BuzzerBox/BuzzController/code/src/rpi_communication.hpp

#ifndef rpi_comm_h
#define rpi_comm_h

#include <Arduino.h>

typedef enum {   
  NO_CONNECTION = 0,
  JUST_CONNECTED = 1,
  CONNECTED = 2,
  JUST_TIMED_OUT = 3,
} Pi_connection_state_t;

typedef struct cmd {
  byte command;
  byte data;
}PiCmd;

class RpiComm {
 public:
  RpiComm(int heartbeatTimeout = 6000);
  boolean checkData();
  void sendUnlock();
  void sendButtonSelected(uint8_t buttonID);
  void sendRawData(byte data);
  Pi_connection_state_t getConnectionState();
  Pi_connection_state_t advanceConnectionState();
  void setConnectionState(Pi_connection_state_t state);
  void heartbeatDetected();
  bool isTimedOut();
  PiCmd getLastCmd();

 private:
  Pi_connection_state_t connection_state;
  unsigned long lastConnection;
  int heartbeatTimeout;
  PiCmd current_command = {0,0};
  uint8_t cmd_fill = 0;

};

#endif
